tasai511/Dragon_Radar/data/3_Star.jpeg

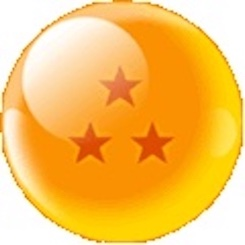
data/3_Star.jpeg
