tasai511/Dragon_Radar/data/reset.jpg

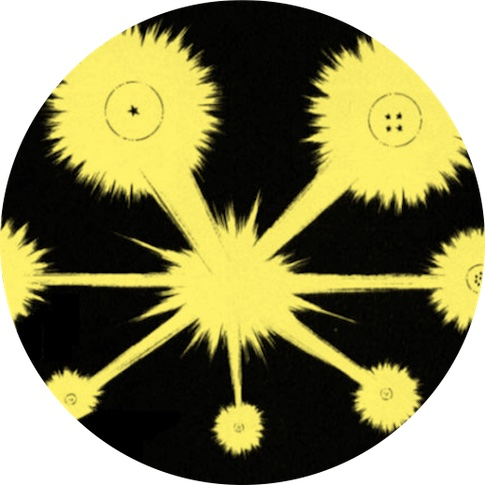
data/reset.jpg
