tasai511/Dragon_Radar/data/1_Star.jpeg

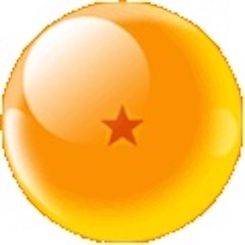
data/1_Star.jpeg
