tasai511/Dragon_Radar/data/2_Star.jpeg

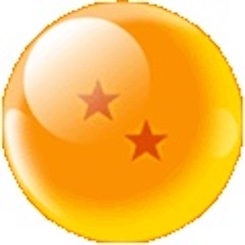
data/2_Star.jpeg
