tasai511/Dragon_Radar/data/4_Star.jpeg

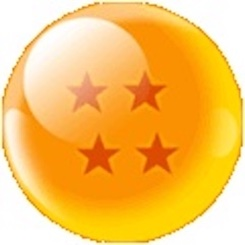
data/4_Star.jpeg
