tasai511/Dragon_Radar/data/5_Star.jpeg

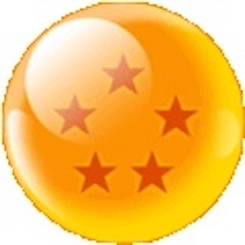
data/5_Star.jpeg
