tasai511/Dragon_Radar/data/7_Star.jpeg

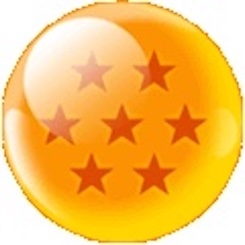
data/7_Star.jpeg
