tasai511/Dragon_Radar/data/Shenron.jpeg

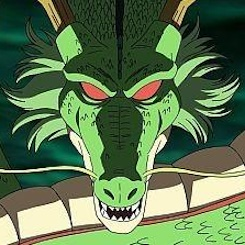
data/Shenron.jpeg
